kanpapa/cosmac_toy_v2/docs/images/cosmac_toy_v2-rev01-prototype.jpg

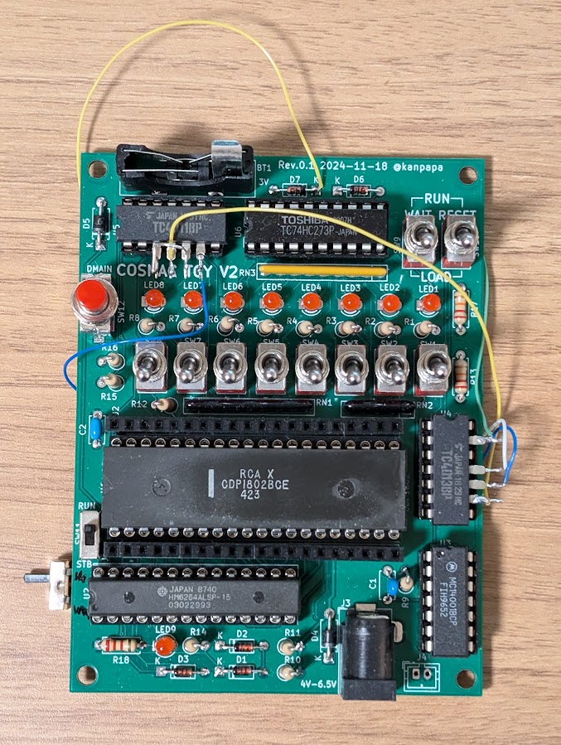
docs/images/cosmac_toy_v2-rev01-prototype.jpg
