kanpapa/cosmac_toy_v2/docs/images/cosmac_toy_v2-rev02-600mil.jpg

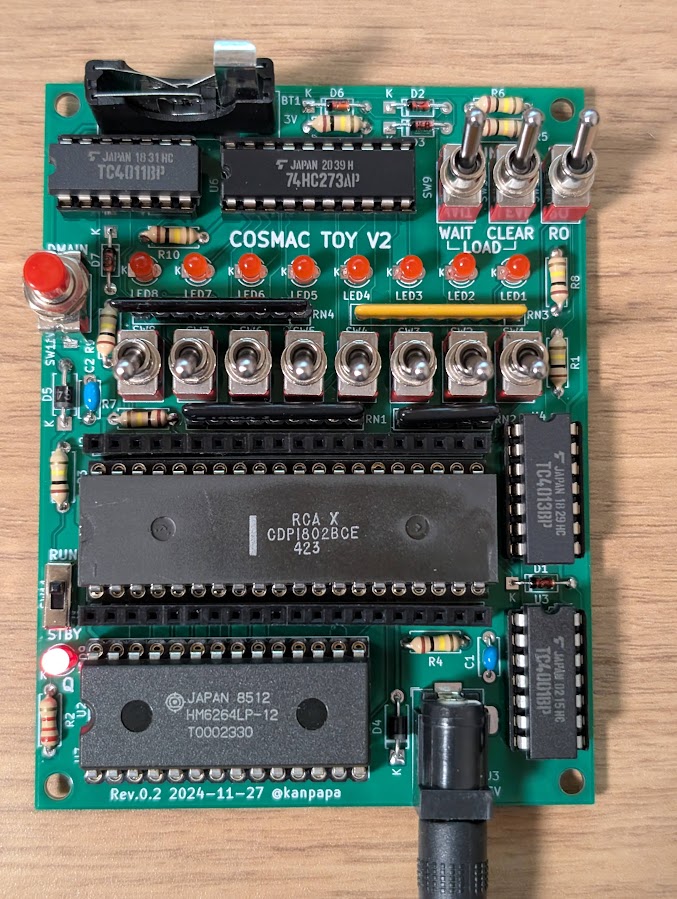
docs/images/cosmac_toy_v2-rev02-600mil.jpg
