kanpapa/cosmac_toy_v2/programs/02_counter1/counter1_thumb.jpg

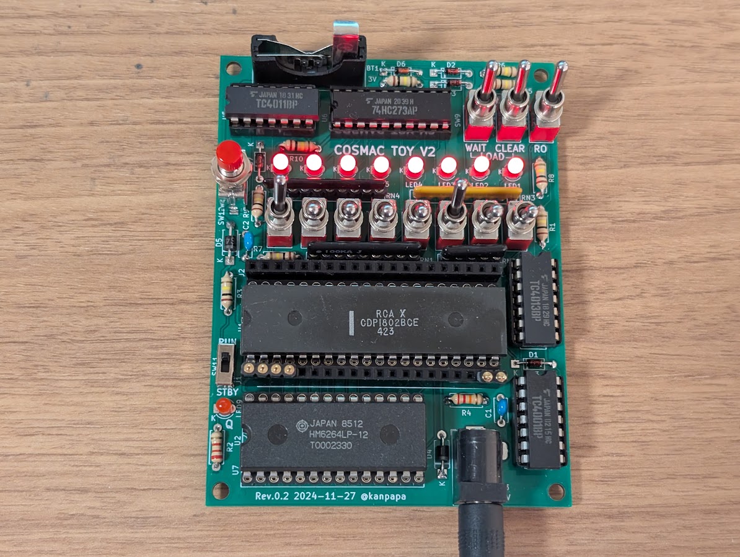
programs/02_counter1/counter1_thumb.jpg
